74th/rp2040-dev-board/rp2040-promicro/rp2040-promicro.jpeg

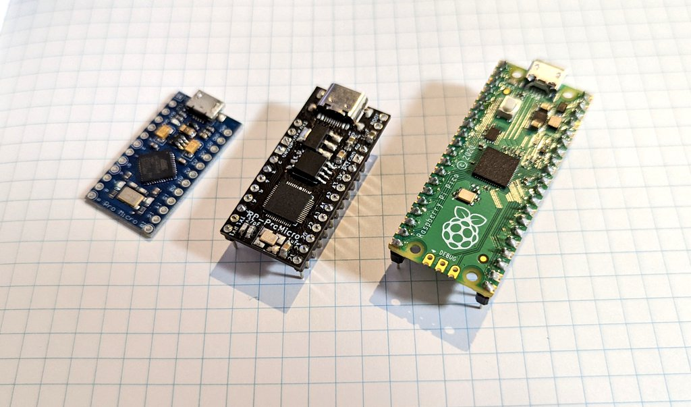
rp2040-promicro/rp2040-promicro.jpeg
